tangles-0/cyberdeck-scout/PCB-Resources/models/Infrared Obstacle Detecting Module v4.step

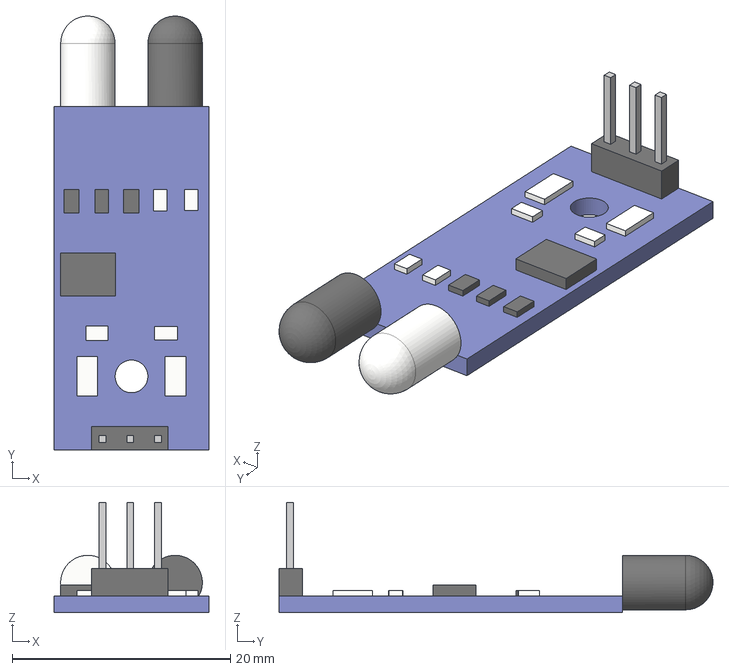
[picture p17: CAD file, 2026-06-25]
PCB-Resources/models/Infrared Obstacle Detecting Module v4.step
14.2 x 39.8 x 10.1 mm
