tangles-0/cyberdeck-scout/PCB-Resources/models/JoyCon Switch Joystick.step

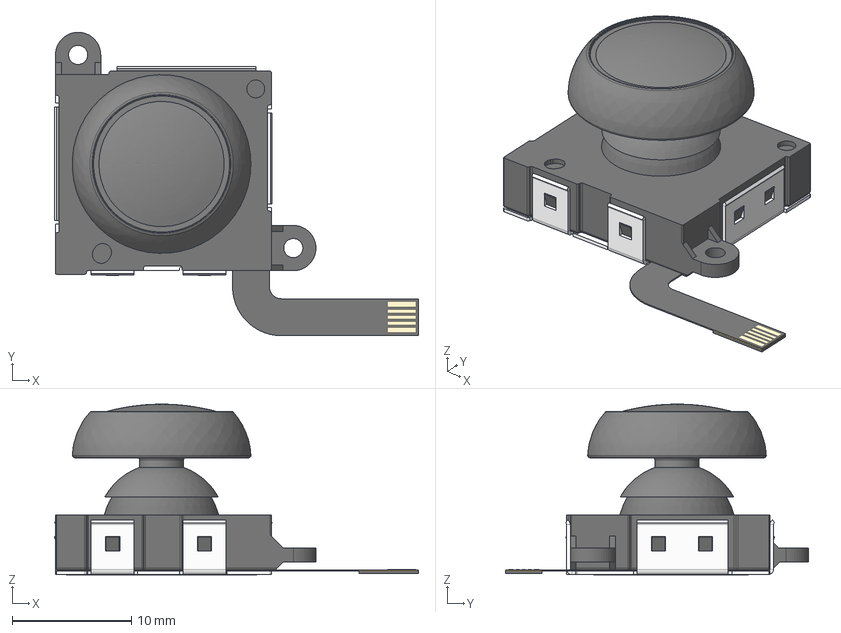
[picture p18: CAD file, 2026-06-25]
PCB-Resources/models/JoyCon Switch Joystick.step
30.5 x 25.5 x 14.3 mm
Handle
Shield
PCB
