tangles-0/cyberdeck-scout/PCB-Resources/models/SIM7100-6-1-15-00-A--3DModel-STEP-56544.STEP

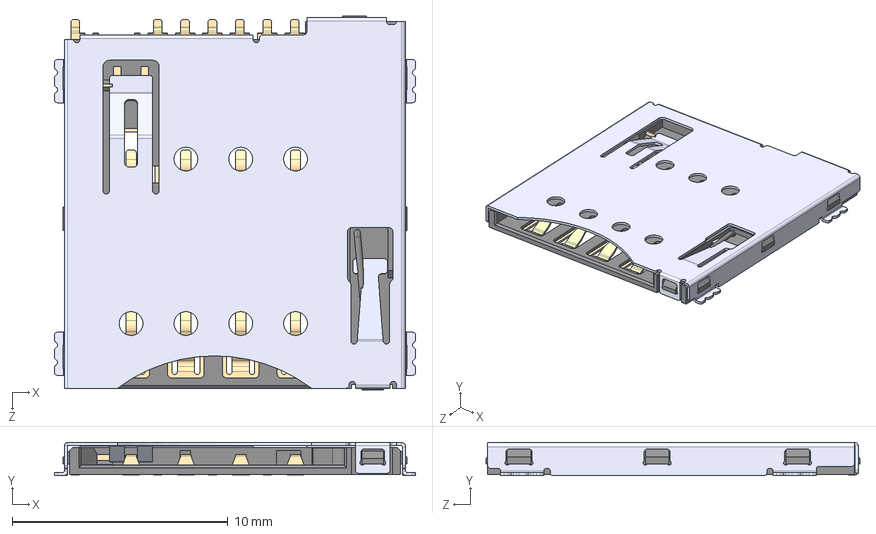
[picture p19: CAD file, 2026-06-25]
PCB-Resources/models/SIM7100-6-1-15-00-A--3DModel-STEP-56544.STEP
16.8 x 1.53 x 17.3 mm
