tangles-0/cyberdeck-scout/PCB-Resources/models/S2B-PH-SM4-TB -LF--SN---3DModel-STEP-269445.STEP

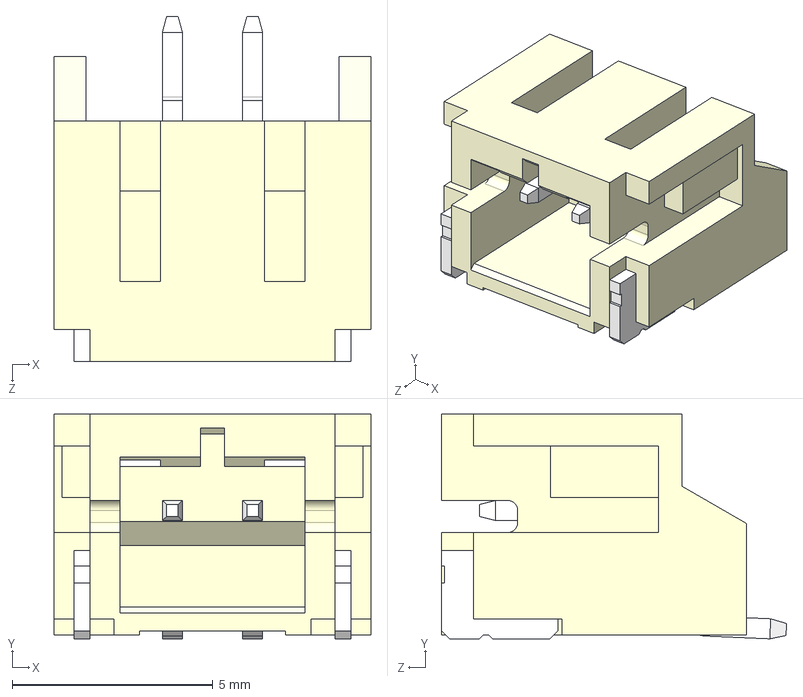
[picture p20: CAD file, 2026-06-25]
PCB-Resources/models/S2B-PH-SM4-TB -LF--SN---3DModel-STEP-269445.STEP
7.90 x 5.60 x 8.60 mm
