tangles-0/cyberdeck-scout/PCB-Resources/models/mini-hdmi-type-C-2013978-2.stp

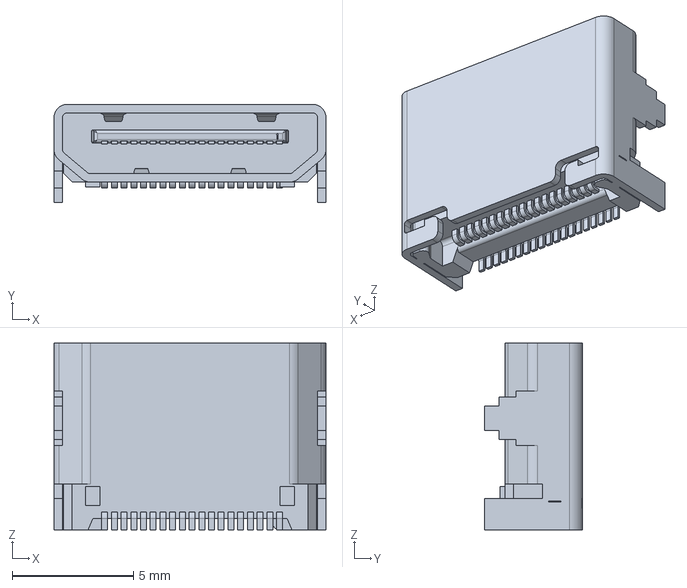
[picture p21: CAD file, 2026-06-25]
PCB-Resources/models/mini-hdmi-type-C-2013978-2.stp
11.2 x 4.05 x 7.70 mm
