tangles-0/cyberdeck-scout/PCB-Resources/models/AFC07-S22FCA-00.stp

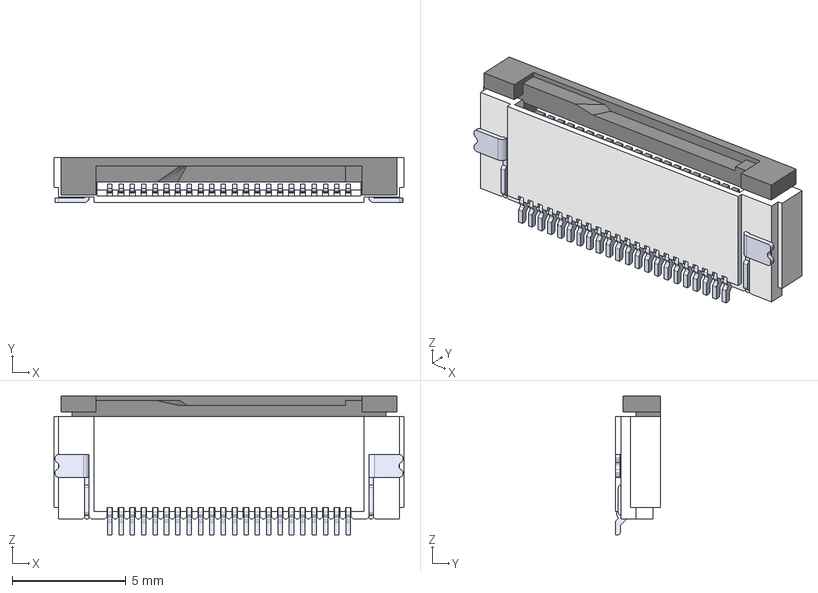
[picture p22: CAD file, 2026-06-25]
PCB-Resources/models/AFC07-S22FCA-00.stp
15.4 x 2.00 x 6.10 mm
