tangles-0/cyberdeck-scout/PCB-Resources/models/modulo heltec ht62_.step

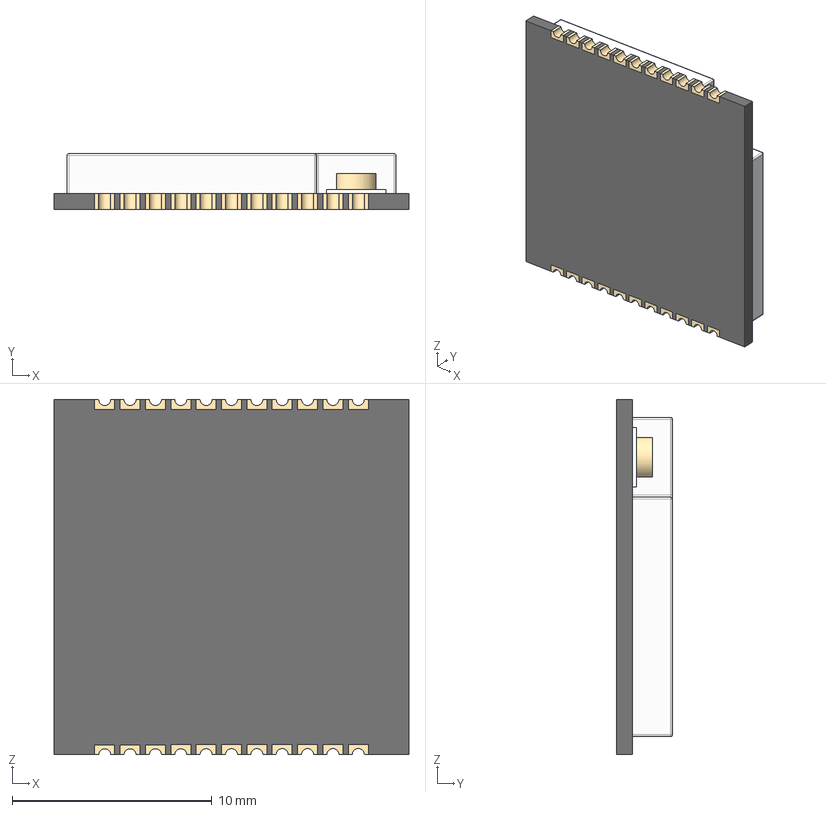
[picture p23: CAD file, 2026-06-25]
PCB-Resources/models/modulo heltec ht62_.step
17.8 x 2.80 x 17.8 mm
