tangles-0/cyberdeck-scout/PCB-Resources/models/WS2812B2020.step

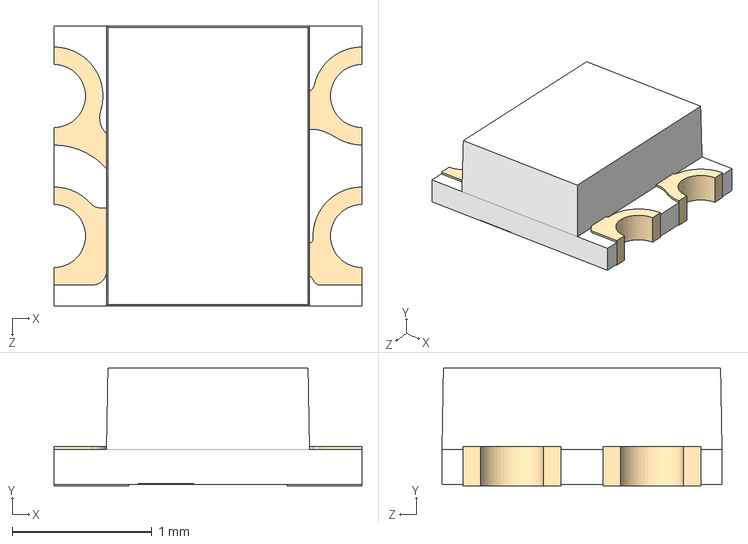
[picture p24: CAD file, 2026-06-25]
PCB-Resources/models/WS2812B2020.step
2.20 x 0.84 x 2.00 mm
