tangles-0/cyberdeck-scout/PCB-Resources/models/BM04B-SRSS-TB.step

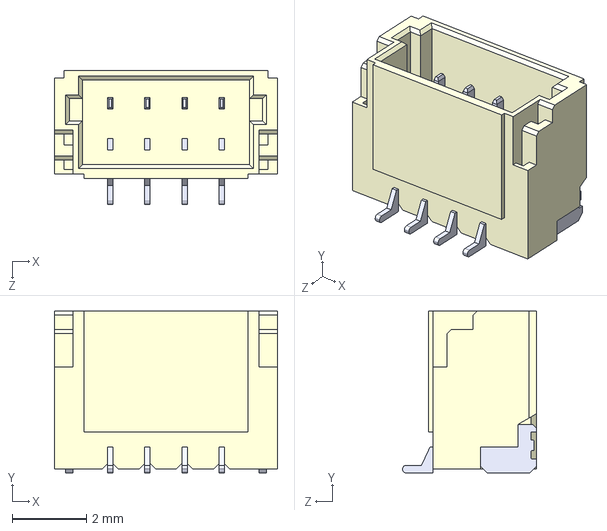
[picture p25: CAD file, 2026-06-25]
PCB-Resources/models/BM04B-SRSS-TB.step
6.00 x 4.35 x 3.60 mm
