tangles-0/cyberdeck-scout/PCB-Resources/models/SSSS811101.step

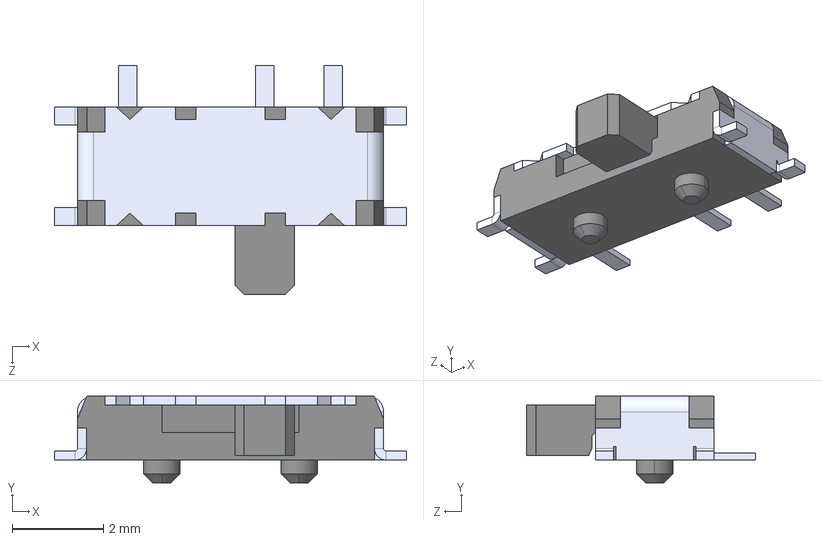
[picture p26: CAD file, 2026-06-25]
PCB-Resources/models/SSSS811101.step
7.70 x 1.90 x 5.00 mm
