tangles-0/cyberdeck-scout/PCB-Resources/models/RCJ-017--3DModel-STEP-1.STEP

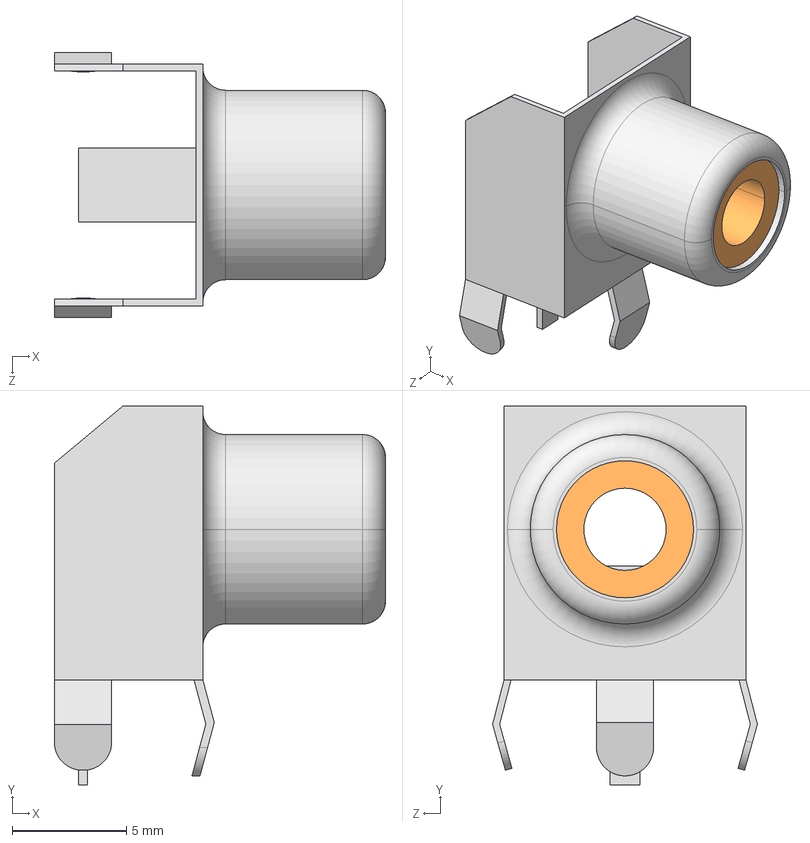
[picture p27: CAD file, 2026-06-25]
PCB-Resources/models/RCJ-017--3DModel-STEP-1.STEP
14.5 x 16.6 x 11.6 mm
