tangles-0/cyberdeck-scout/PCB-Resources/models/SMF05C.step

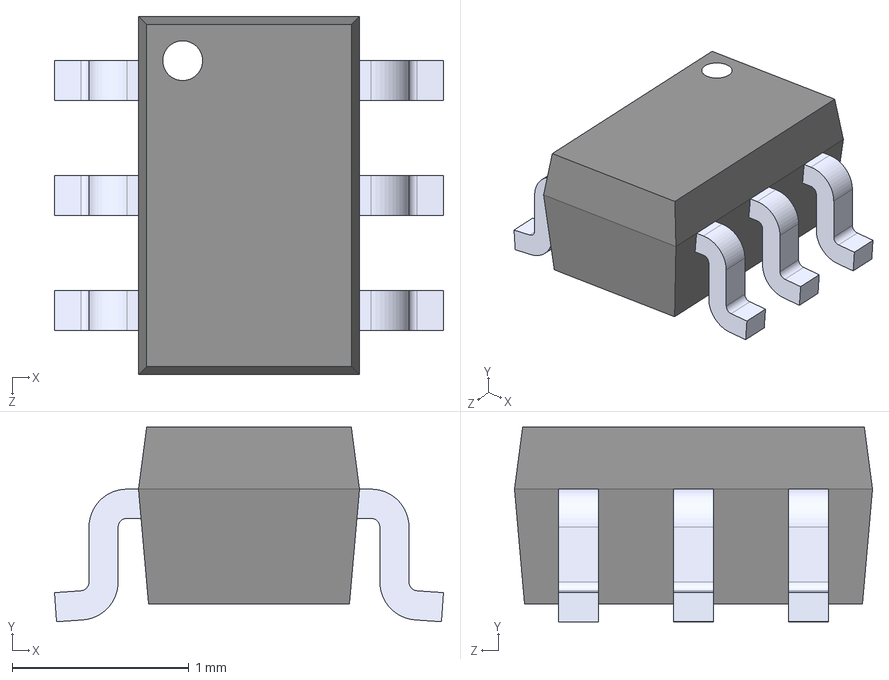
[picture p28: CAD file, 2026-06-25]
PCB-Resources/models/SMF05C.step
2.20 x 1.10 x 2.03 mm
