tangles-0/cyberdeck-scout/PCB-Resources/models/PCM2704CDB.step

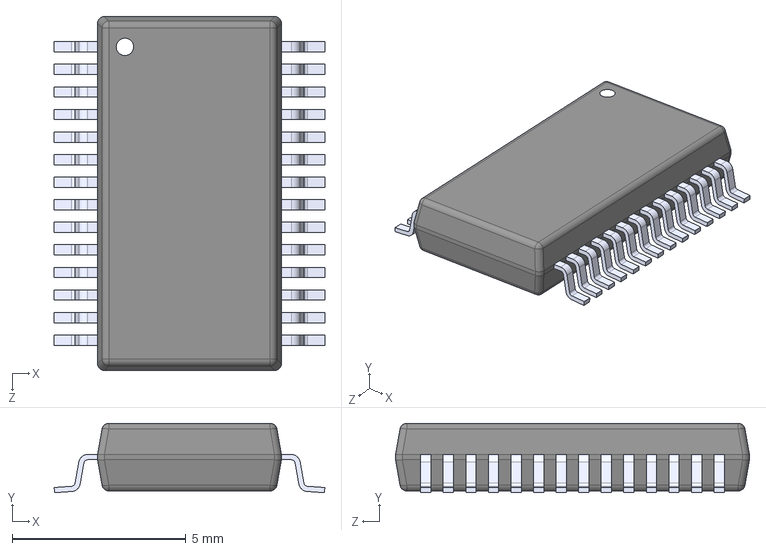
[picture p29: CAD file, 2026-06-25]
PCB-Resources/models/PCM2704CDB.step
7.80 x 2.00 x 10.2 mm
