tangles-0/cyberdeck-scout/PCB-Resources/models/AFC07-S30FCA-00.stp

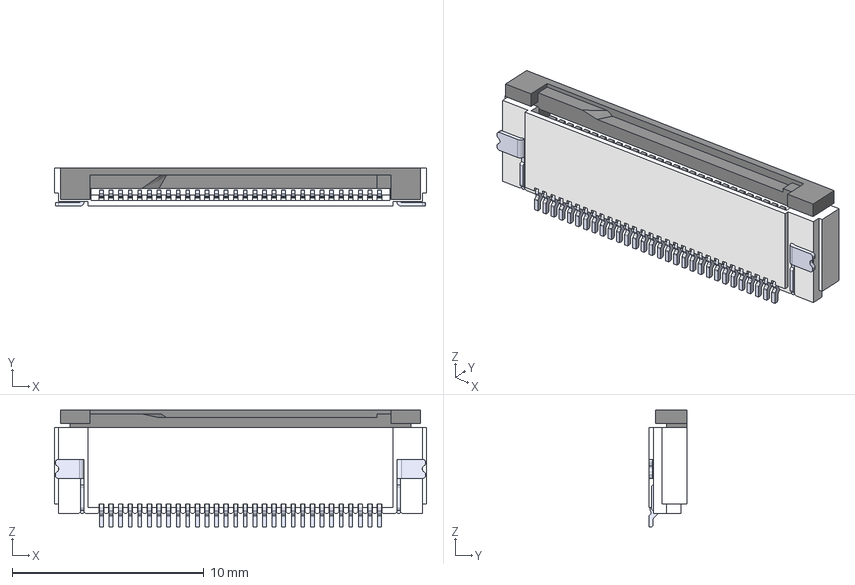
[picture p30: CAD file, 2026-06-25]
PCB-Resources/models/AFC07-S30FCA-00.stp
19.4 x 2.00 x 6.10 mm
