tangles-0/cyberdeck-scout/PCB-Resources/models/QFN40P400X400X100-33N.step

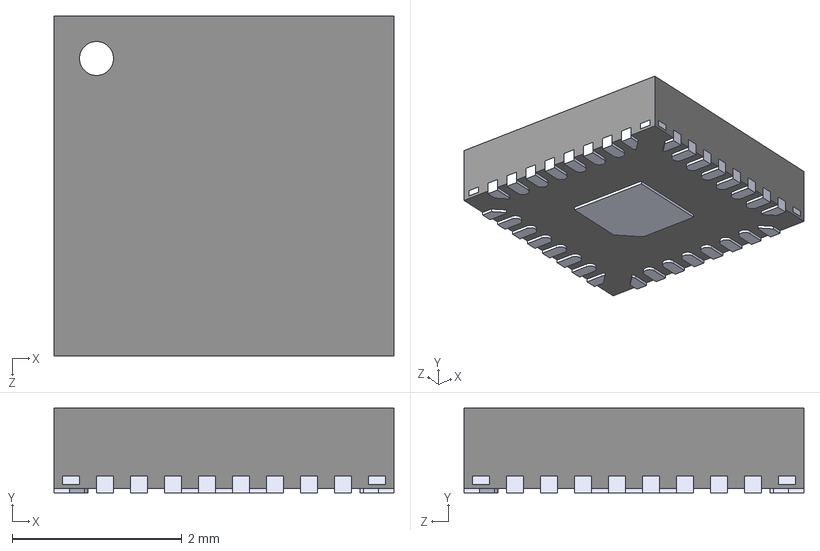
[picture p31: CAD file, 2026-06-25]
PCB-Resources/models/QFN40P400X400X100-33N.step
4.00 x 1.00 x 4.00 mm
