tangles-0/cyberdeck-scout/PCB-Resources/models/1000base-t-magnetics.stp

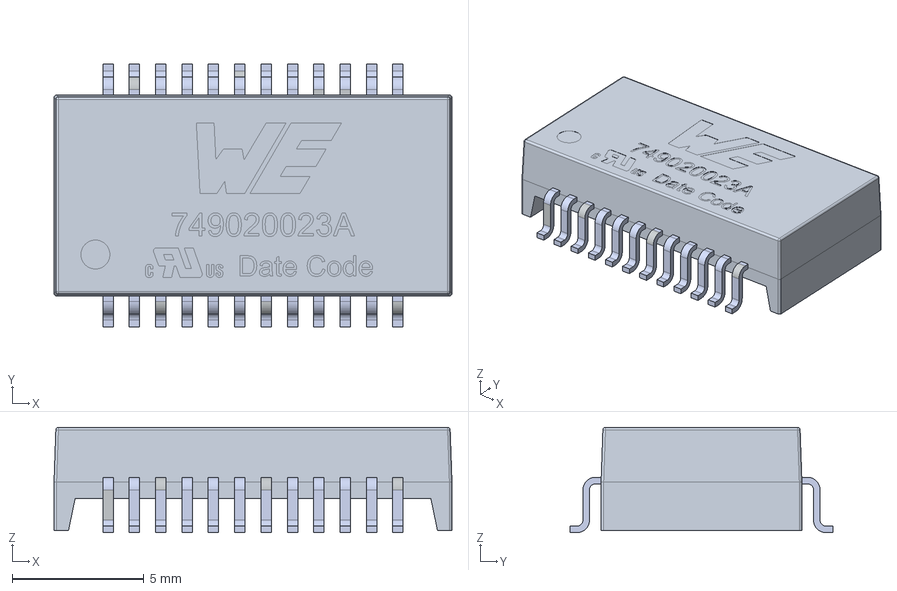
[picture p32: CAD file, 2026-06-25]
PCB-Resources/models/1000base-t-magnetics.stp
15.1 x 10.0 x 4.00 mm
Housing_oa_0
Pins
