tangles-0/cyberdeck-scout/PCB-Resources/models/cyntec_vcmt063t.step

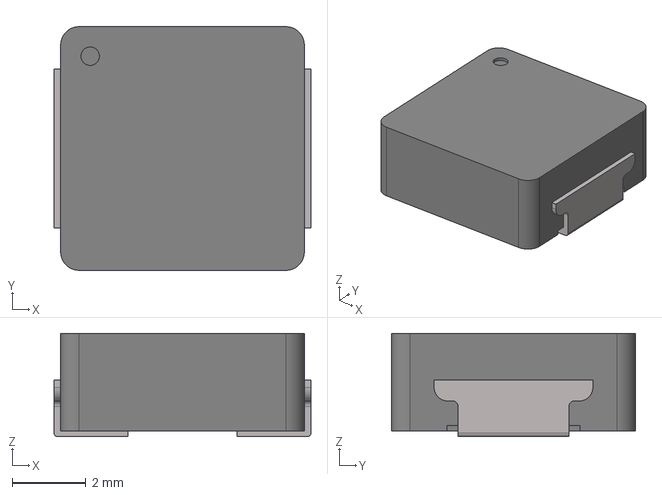
[picture p33: CAD file, 2026-06-25]
PCB-Resources/models/cyntec_vcmt063t.step
6.96 x 6.60 x 2.80 mm
