tangles-0/cyberdeck-scout/PCB-Resources/models/FPC-5.stp

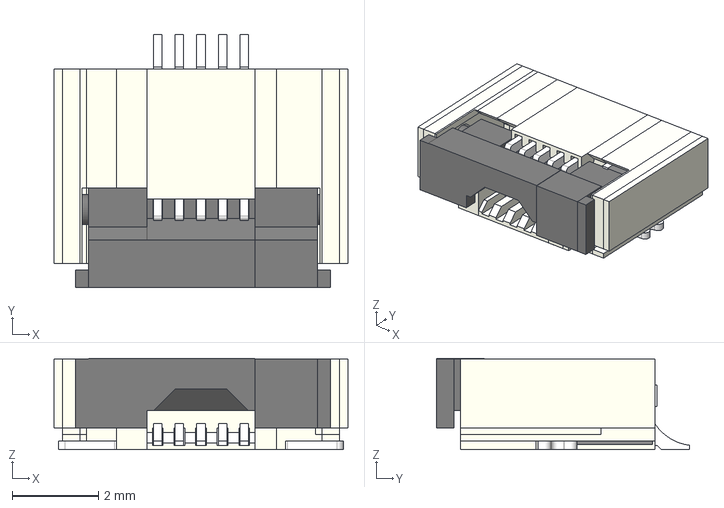
[picture p35: CAD file, 2026-06-25]
PCB-Resources/models/FPC-5.stp
6.80 x 5.85 x 2.11 mm
