tangles-0/cyberdeck-scout/PCB-Resources/models/PspJoystick v5.step

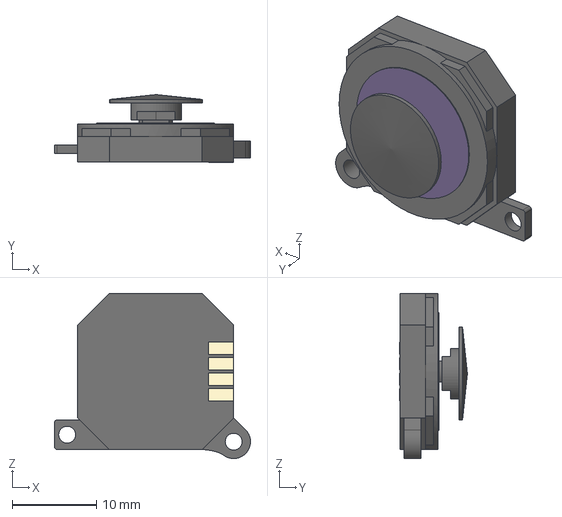
[picture p36: CAD file, 2026-06-25]
PCB-Resources/models/PspJoystick v5.step
23.2 x 8.05 x 19.6 mm
