tangles-0/cyberdeck-scout/PCB-Resources/models/PC817X2NIP1B.step

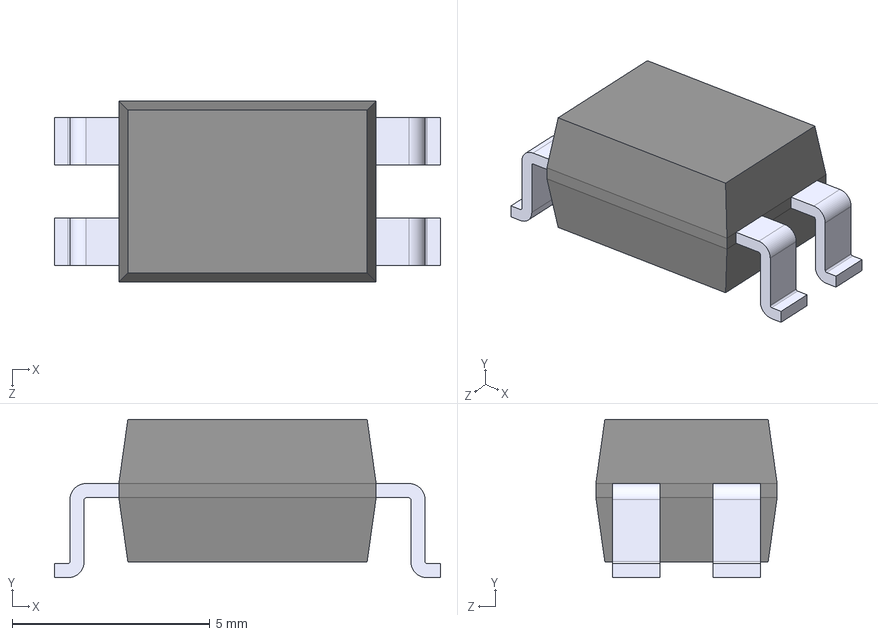
[picture p37: CAD file, 2026-06-25]
PCB-Resources/models/PC817X2NIP1B.step
9.75 x 4.00 x 4.58 mm
