tangles-0/cyberdeck-scout/PCB-Resources/models/PCM2706CPJT.step

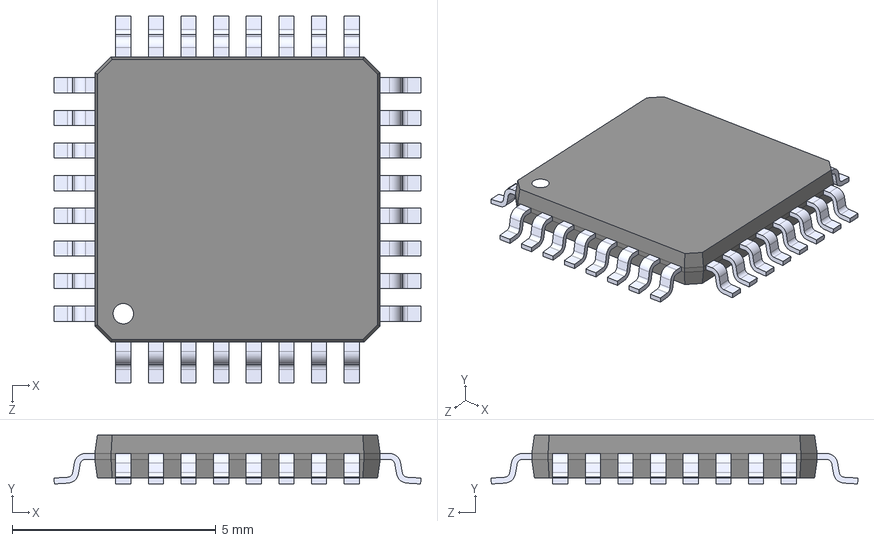
[picture p38: CAD file, 2026-06-25]
PCB-Resources/models/PCM2706CPJT.step
9.00 x 1.20 x 9.00 mm
