tangles-0/cyberdeck-scout/PCB-Resources/models/LQFP_0.5P_100.STEP

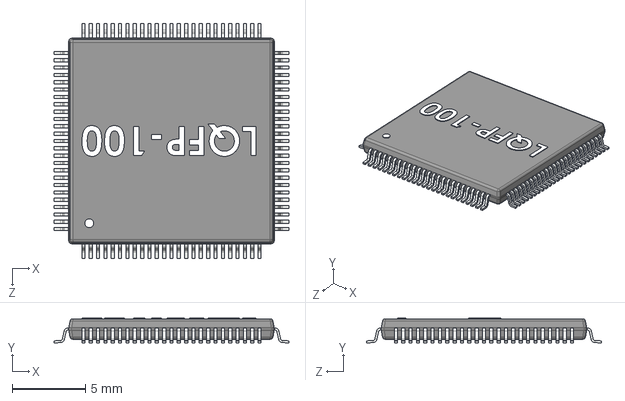
[picture p39: CAD file, 2026-06-25]
PCB-Resources/models/LQFP_0.5P_100.STEP
16.0 x 1.70 x 16.0 mm
