tangles-0/cyberdeck-scout/PCB-Resources/models/TPD2EUSB30DRTR.step

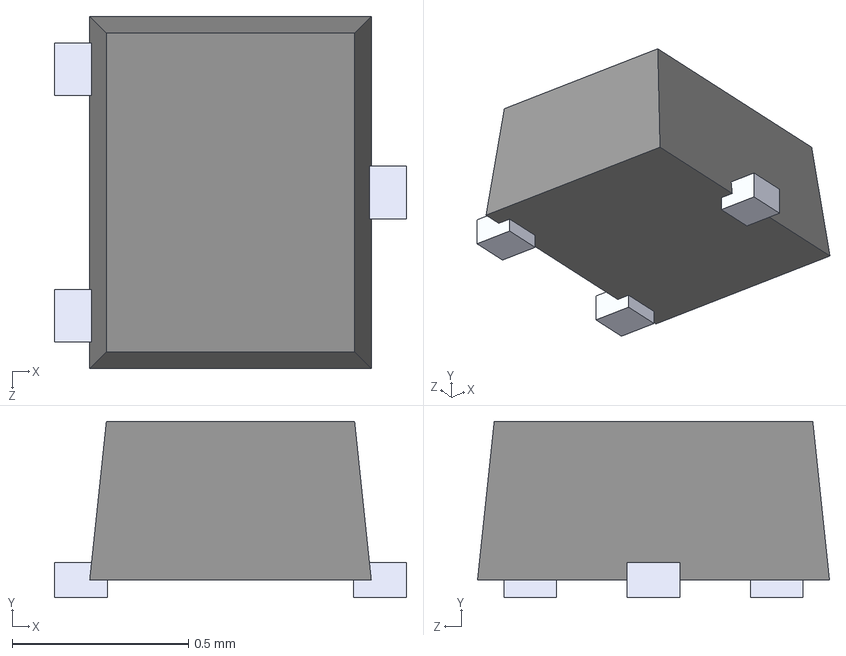
[picture p40: CAD file, 2026-06-25]
PCB-Resources/models/TPD2EUSB30DRTR.step
1.00 x 0.5 x 1.00 mm
