tangles-0/cyberdeck-scout/PCB-Resources/models/PJ311D_WPos.STEP

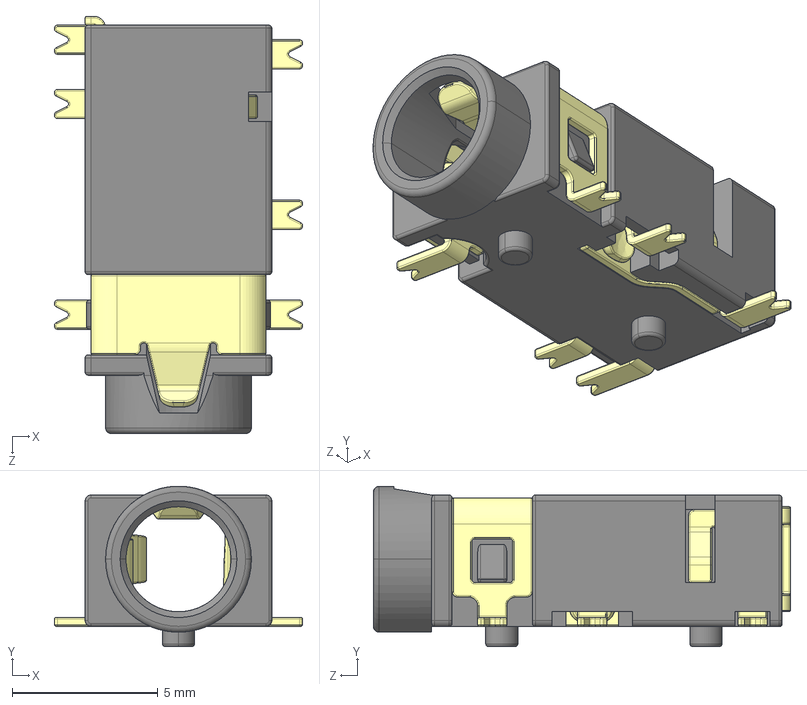
[picture p41: CAD file, 2026-06-25]
PCB-Resources/models/PJ311D_WPos.STEP
8.50 x 5.50 x 14.3 mm
001^PJ311D_WPos
002^PJ311D_WPos
003^PJ311D_WPos
004^PJ311D_WPos
005^PJ311D_WPos
006^PJ311D_WPos
007^PJ311D_WPos
