tangles-0/cyberdeck-scout/PCB-Resources/models/1-2199119-5.step

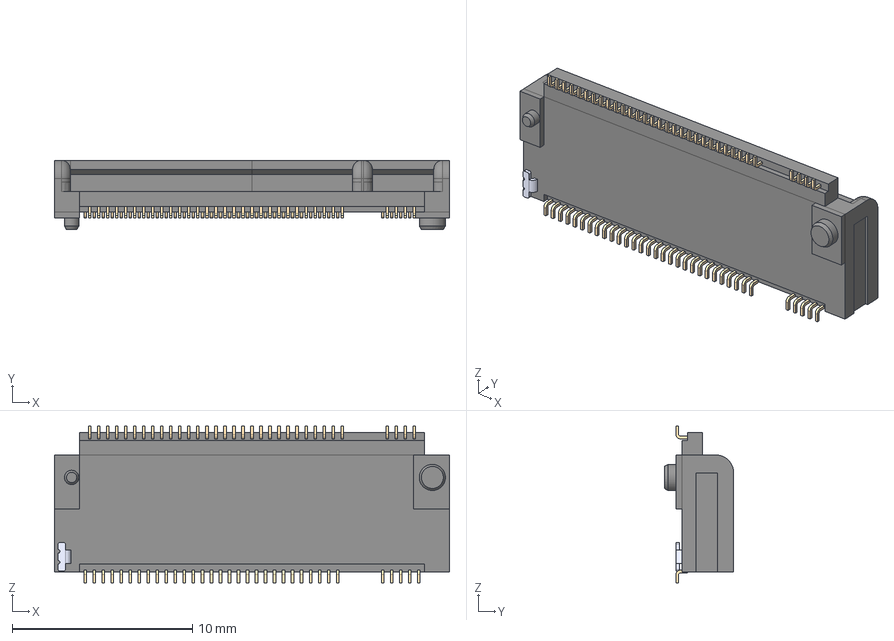
[picture p42: CAD file, 2026-06-25]
PCB-Resources/models/1-2199119-5.step
21.9 x 3.85 x 8.70 mm
Body005 (Mirror #1)
