tangles-0/cyberdeck-scout/PCB-Resources/models/QFN26 4mm X 4mm.STEP

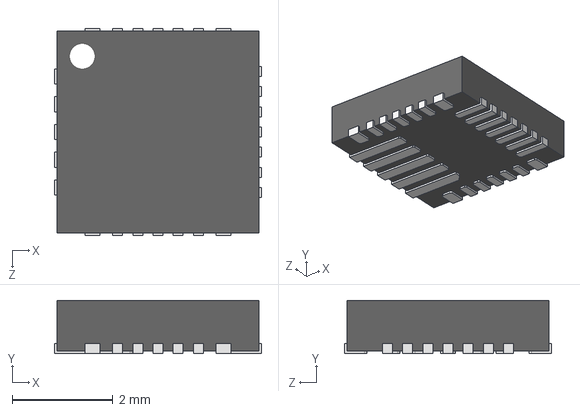
[picture p43: CAD file, 2026-06-25]
PCB-Resources/models/QFN26 4mm X 4mm.STEP
4.10 x 1.05 x 4.10 mm
