tangles-0/cyberdeck-scout/PCB-Resources/models/4_3inch-dsi-lcd-V1.stp

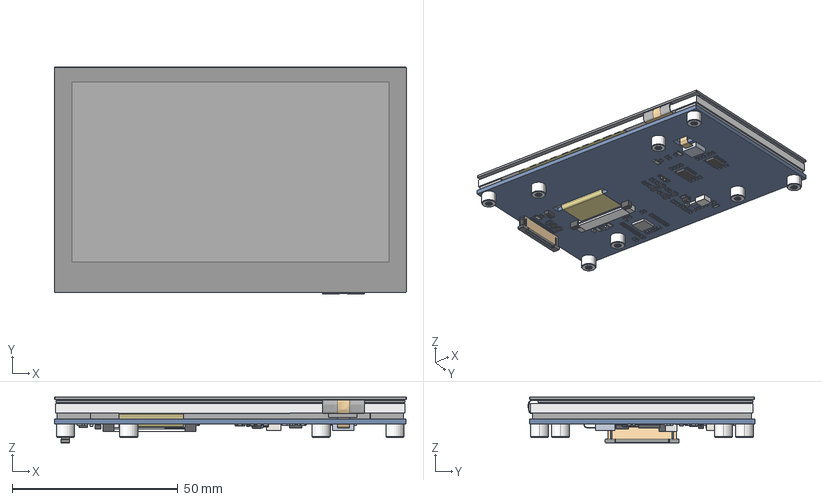
[picture p44: CAD file, 2026-06-25]
PCB-Resources/models/4_3inch-dsi-lcd-V1.stp
106.1 x 68.4 x 13.8 mm
43H-800480-IPS
43H-800480-TP
BOARD
_2_1_2_3_4_AF0 x 2
_7_1_2_AF0 x 2
3_1_2_A x 2
EXTRUDED-91008 x 5
EXTRUDED-91380 x 10
EXTRUDED-91788 x 2
EXTRUDED-92160 x 4
EXTRUDED-92614 x 26
EXTRUDED-92986 x 54
EXTRUDED-93762 x 8
EXTRUDED-94134 x 16
EXTRUDED-95370 x 28
EXTRUDED-95742 x 56
EXTRUDED-96150 x 26
EXTRUDED-96522 x 52
EXTRUDED-96930
EXTRUDED-98589 x 12
EXTRUDED-98961 x 4
EXTRUDED-99531 x 5
EXTRUDED-100568 x 2
EXTRUDED-101876 x 40
EXTRUDED-102630
CIRCUITWORKS-SOD123 x 2
EXTRUDED-106278
EXTRUDED-106739
EXTRUDED-107111 x 2
EXTRUDED-107488
EXTRUDED-107860 x 2
EXTRUDED-108430
EXTRUDED-108972
EXTRUDED-109367 x 3
SMTSO-M2_5-4ET x 8
DISPLAY_CAM
TP-CONNECTOR
EVA-2MM
