tangles-0/cyberdeck-scout/PCB-Resources/models/reverse-mount-LED.STEP

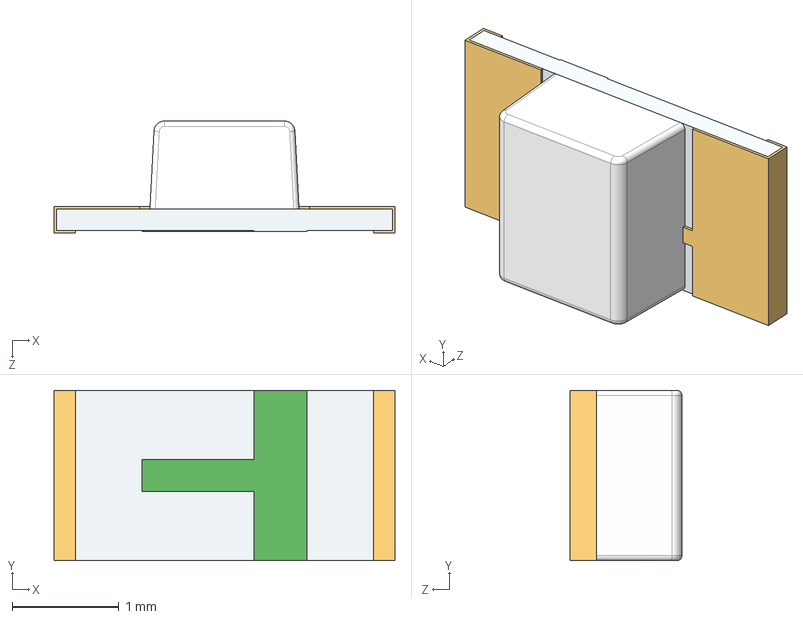
[picture p45: CAD file, 2026-06-25]
PCB-Resources/models/reverse-mount-LED.STEP
3.20 x 1.60 x 1.05 mm
KPTR-3216CGCK
KPTR-3216CGCK-e2
KPTR-3216CGCK-g
KPTR-3216CGCK-e
