tangles-0/cyberdeck-scout/PCB-Resources/models/B2B-PH-SM4-TB--3DModel-STEP-418109.STEP

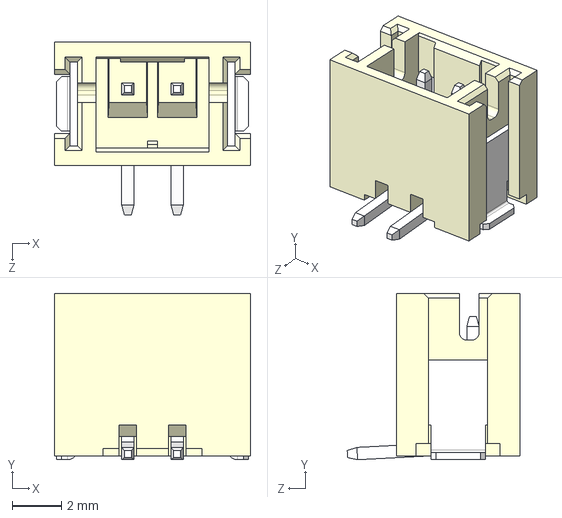
[picture p46: CAD file, 2026-06-25]
PCB-Resources/models/B2B-PH-SM4-TB--3DModel-STEP-418109.STEP
7.95 x 6.75 x 7.00 mm
