tangles-0/cyberdeck-scout/PCB-Resources/models/RAK4630.step

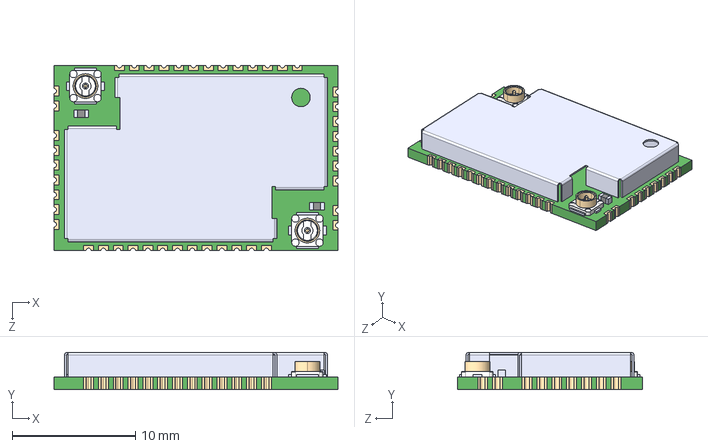
[picture p47: CAD file, 2026-06-25]
PCB-Resources/models/RAK4630.step
23.0 x 3.00 x 15.0 mm
