tangles-0/cyberdeck-scout/PCB-Resources/models/ss-12d11g5r.stp

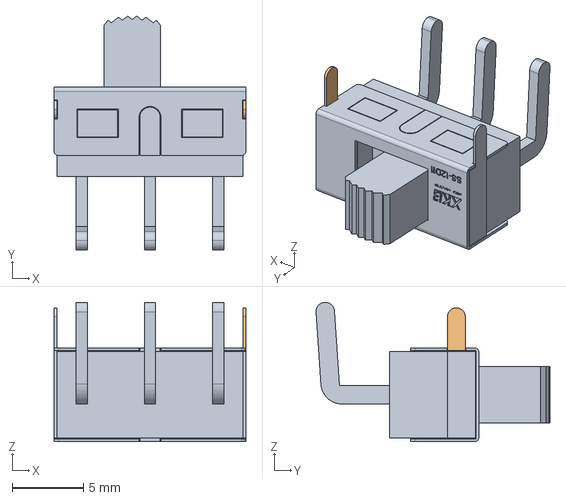
[picture p48: CAD file, 2026-06-25]
PCB-Resources/models/ss-12d11g5r.stp
13.5 x 16.4 x 9.80 mm
