tangles-0/cyberdeck-scout/PCB-Resources/models/QFN-28 (4x4x0.9).step

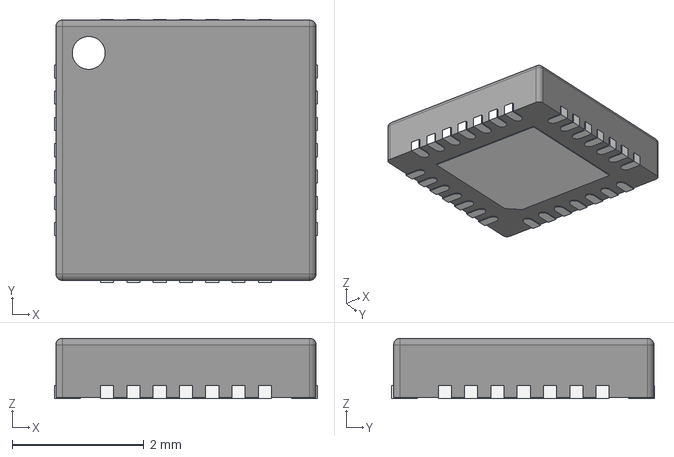
[picture p49: CAD file, 2026-06-25]
PCB-Resources/models/QFN-28 (4x4x0.9).step
4.00 x 4.00 x 0.92 mm
