tangles-0/cyberdeck-scout/PCB-Resources/models/TS-1088-AR02016--3DModel-STEP-269445.STEP

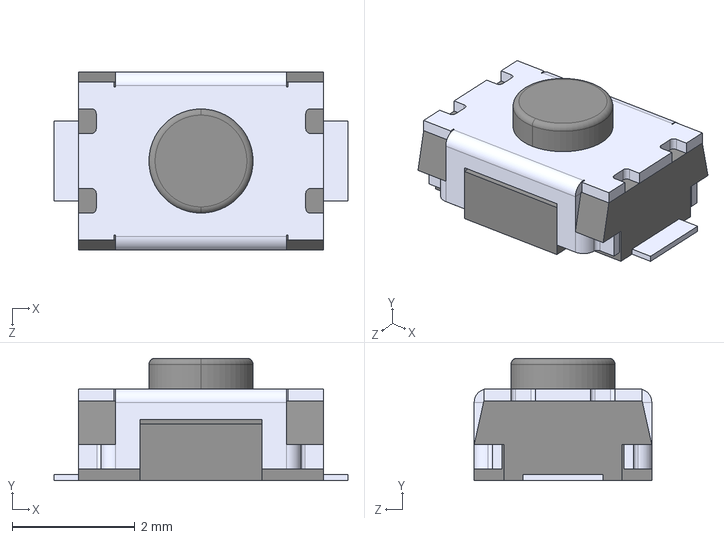
[picture p50: CAD file, 2026-06-25]
PCB-Resources/models/TS-1088-AR02016--3DModel-STEP-269445.STEP
4.80 x 2.00 x 2.90 mm
