tangles-0/cyberdeck-scout/PCB-Resources/models/SO-8EP.STP

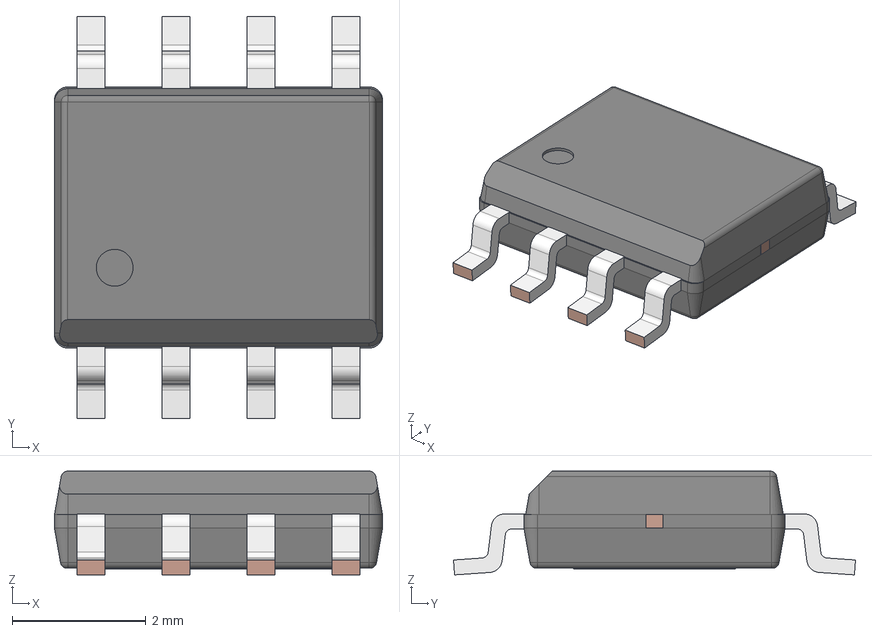
[picture p51: CAD file, 2026-06-25]
PCB-Resources/models/SO-8EP.STP
4.90 x 6.00 x 1.55 mm
CPD
LDF - outer lead
LDF - 8L-EP
