tangles-0/cyberdeck-scout/PCB-Resources/models/2-1734839-0.stp

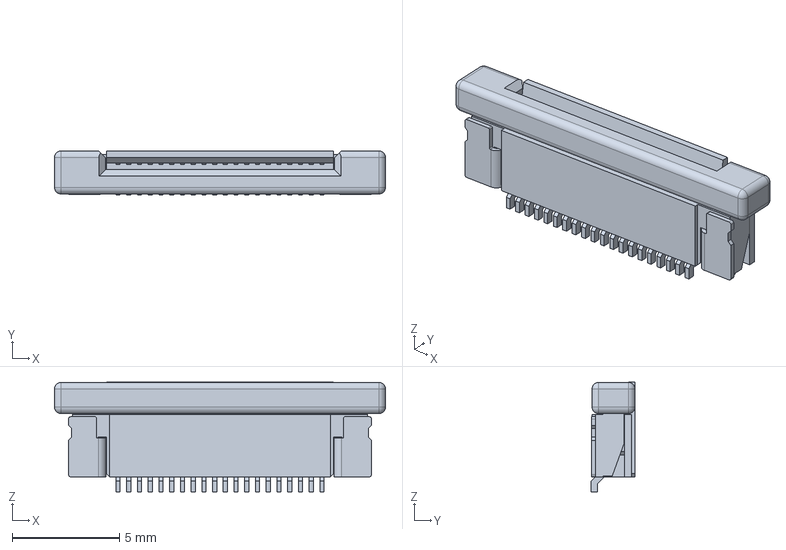
[picture p52: CAD file, 2026-06-25]
PCB-Resources/models/2-1734839-0.stp
15.4 x 2.05 x 5.11 mm
