tangles-0/cyberdeck-scout/PCB-Resources/models/Keystone10mmDiaDomePB v2.step

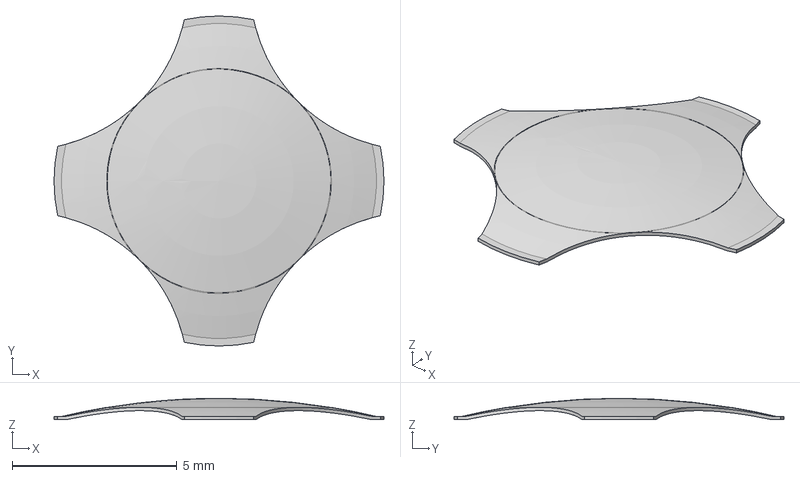
[picture p53: CAD file, 2026-06-25]
PCB-Resources/models/Keystone10mmDiaDomePB v2.step
10.0 x 10.0 x 0.65 mm
