tangles-0/cyberdeck-scout/PCB-Resources/models/TPD4EUSB30DQAR.step

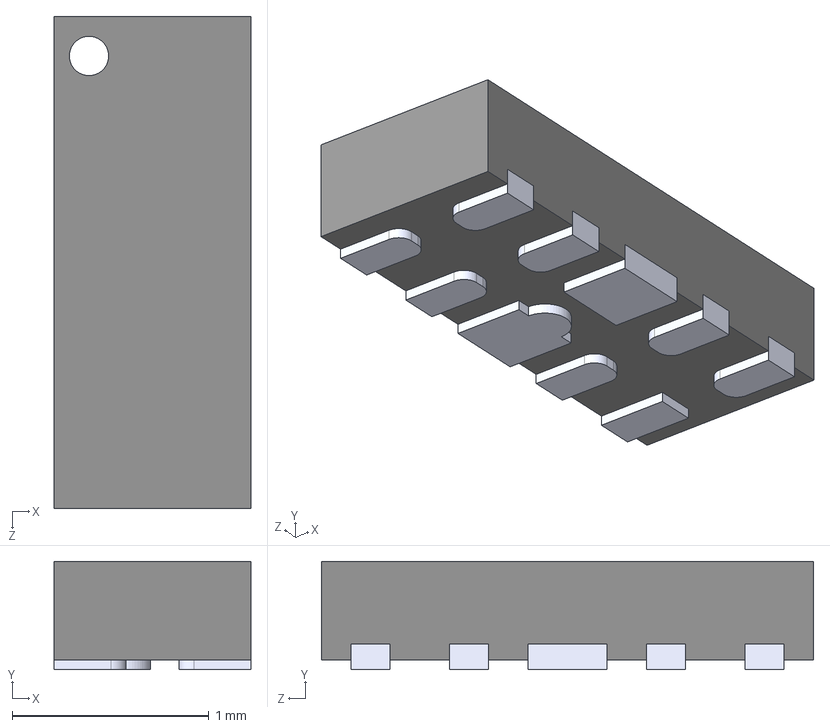
[picture p54: CAD file, 2026-06-25]
PCB-Resources/models/TPD4EUSB30DQAR.step
1.00 x 0.55 x 2.50 mm
