tangles-0/cyberdeck-scout/PCB-Resources/models/QFN26-3.5x3.5-MP2723GQC.step

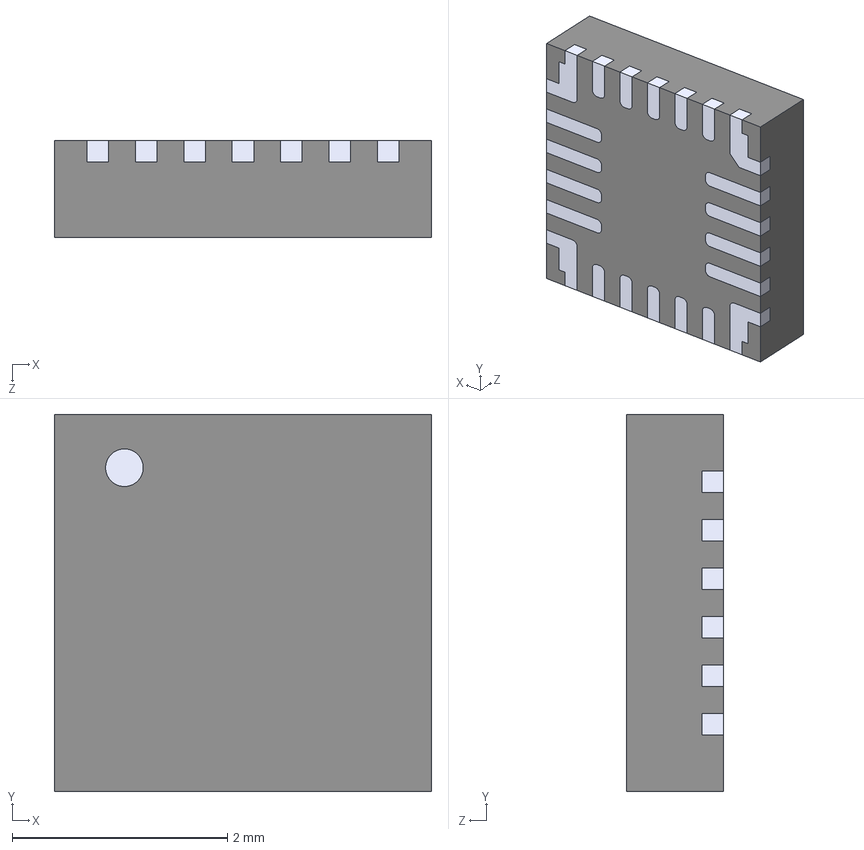
[picture p55: CAD file, 2026-06-25]
PCB-Resources/models/QFN26-3.5x3.5-MP2723GQC.step
3.50 x 3.50 x 0.9 mm
