tangles-0/cyberdeck-scout/PCB-Resources/models/FTE-121-01-G-DH-K.stp

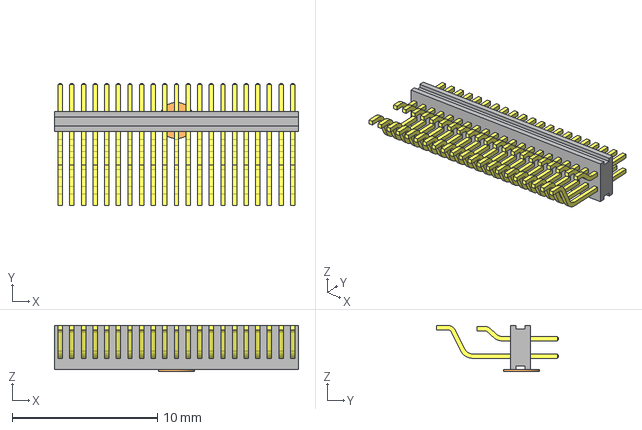
[picture p56: CAD file, 2026-06-25]
PCB-Resources/models/FTE-121-01-G-DH-K.stp
16.8 x 8.38 x 3.20 mm
FTE-121-01-G-DH-K_body
FTE-121-01-G-DH-K_pins
