tangles-0/cyberdeck-scout/PCB-Resources/models/HRO_TYPE-C-31-M-12.step

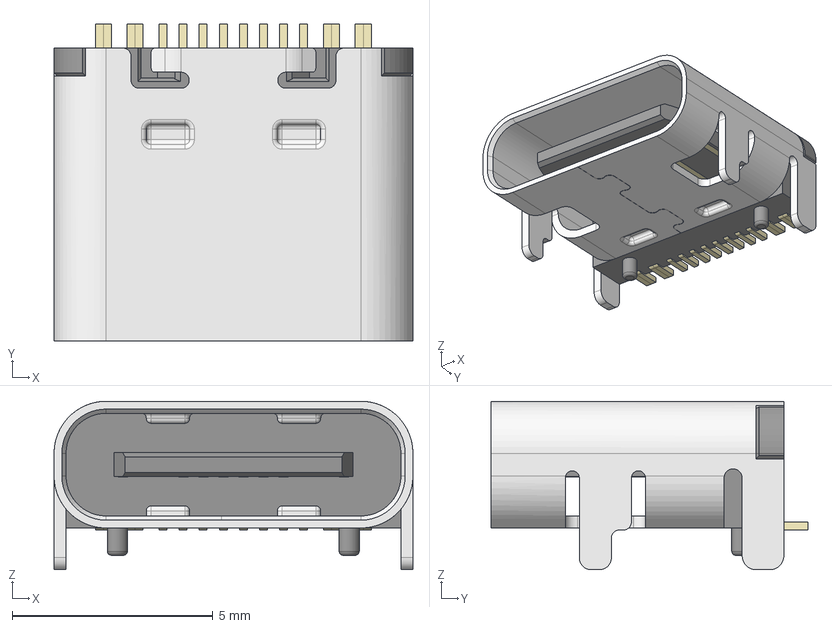
[picture p57: CAD file, 2026-06-25]
PCB-Resources/models/HRO_TYPE-C-31-M-12.step
8.95 x 7.90 x 4.20 mm
