tangles-0/cyberdeck-scout/PCB-Resources/models/DM3AT-SF-PEJM5.step

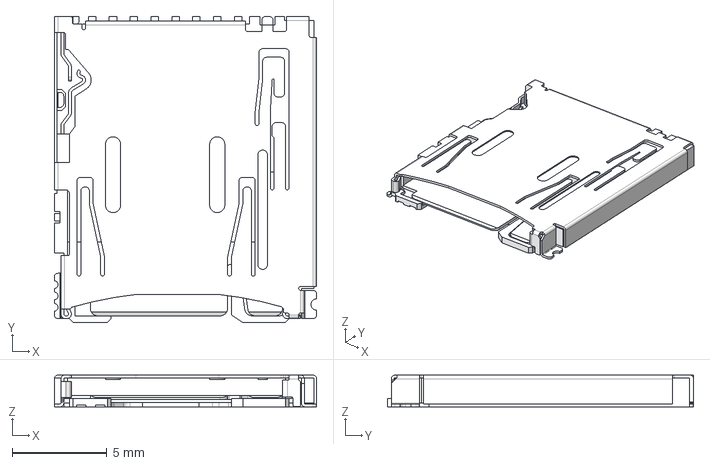
[picture p58: CAD file, 2026-06-25]
PCB-Resources/models/DM3AT-SF-PEJM5.step
13.8 x 16.2 x 1.68 mm
