tangles-0/cyberdeck-scout/PCB-Resources/models/AFC07-S05FCA-00.stp

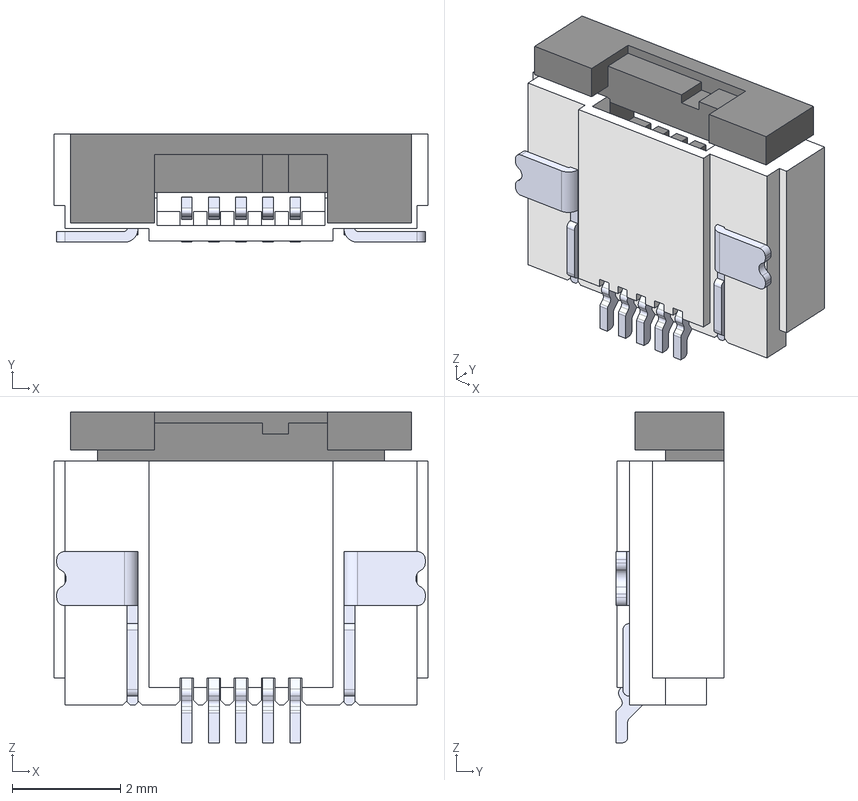
[picture p59: CAD file, 2026-06-25]
PCB-Resources/models/AFC07-S05FCA-00.stp
6.90 x 2.00 x 6.10 mm
