tangles-0/cyberdeck-scout/PCB-Resources/models/TL 3330 Tactile Button.stp

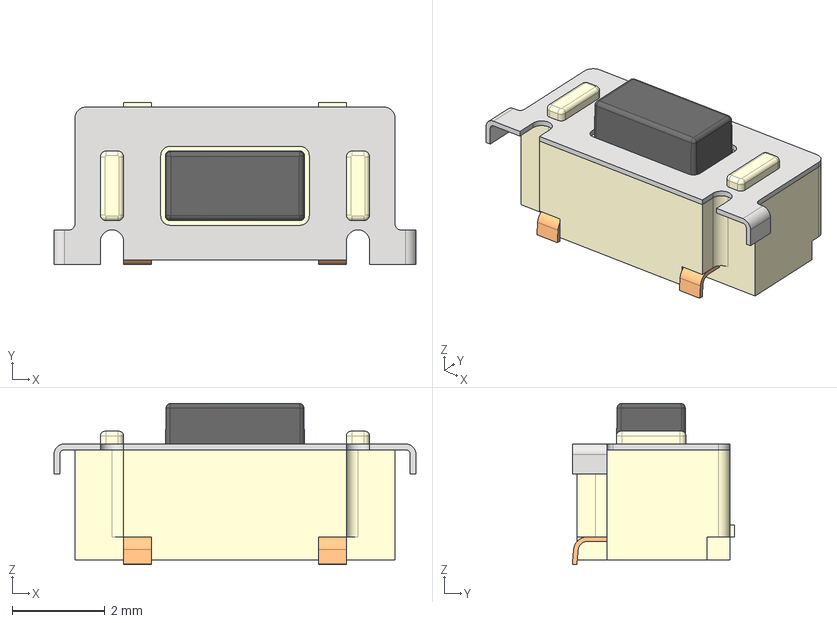
[picture p60: CAD file, 2026-06-25]
PCB-Resources/models/TL 3330 Tactile Button.stp
7.80 x 3.50 x 3.48 mm
