tangles-0/cyberdeck-scout/PCB-Resources/models/MP2632B.step

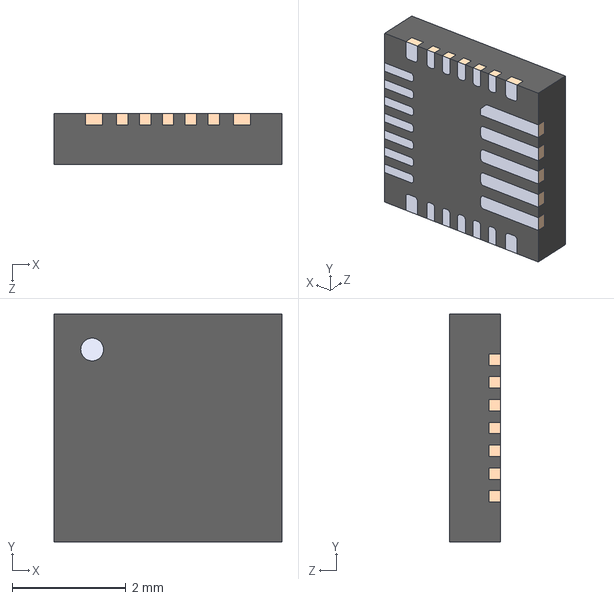
[picture p61: CAD file, 2026-06-25]
PCB-Resources/models/MP2632B.step
4.00 x 4.00 x 0.9 mm
