tangles-0/cyberdeck-scout/PCB-Resources/models/XFL4020-102MEC.step

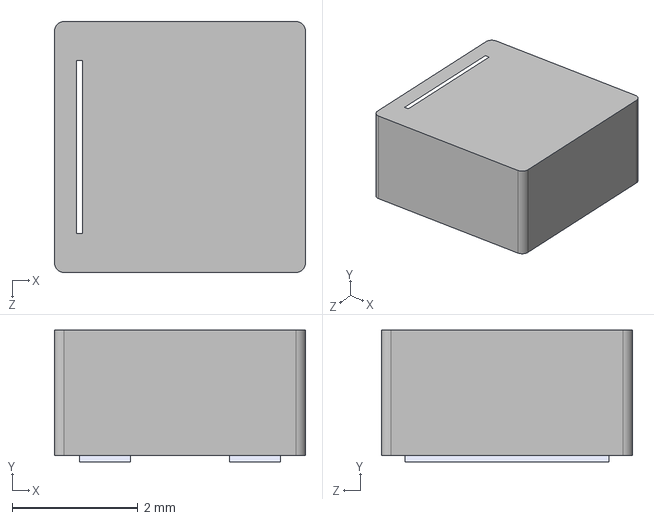
[picture p62: CAD file, 2026-06-25]
PCB-Resources/models/XFL4020-102MEC.step
4.00 x 2.10 x 4.00 mm
