tangles-0/cyberdeck-scout/PCB-Resources/models/AFC01-S40FCA-00.step

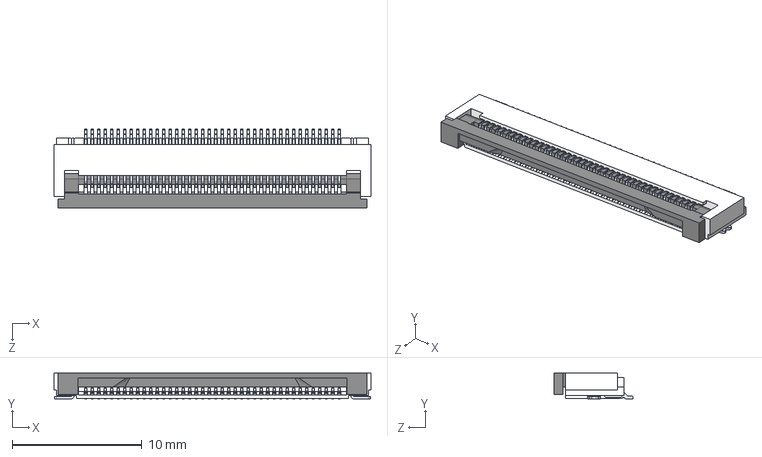
[picture p63: CAD file, 2026-06-25]
PCB-Resources/models/AFC01-S40FCA-00.step
24.4 x 2.00 x 6.10 mm
