tangles-0/cyberdeck-scout/PCB-Resources/models/RK10J1_E.STEP

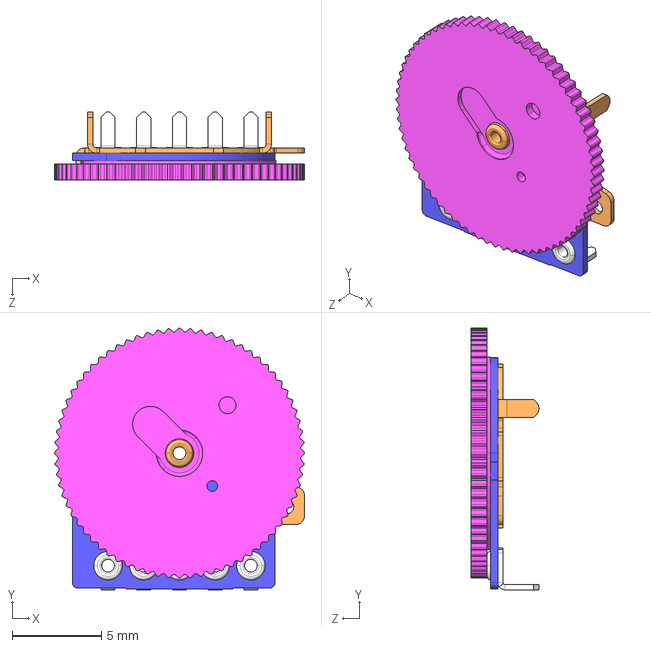
[picture p64: CAD file, 2026-06-25]
PCB-Resources/models/RK10J1_E.STEP
14.0 x 14.6 x 3.80 mm
