tangles-0/cyberdeck-scout/PCB-Resources/models/TUSB8042AIRGCR.step

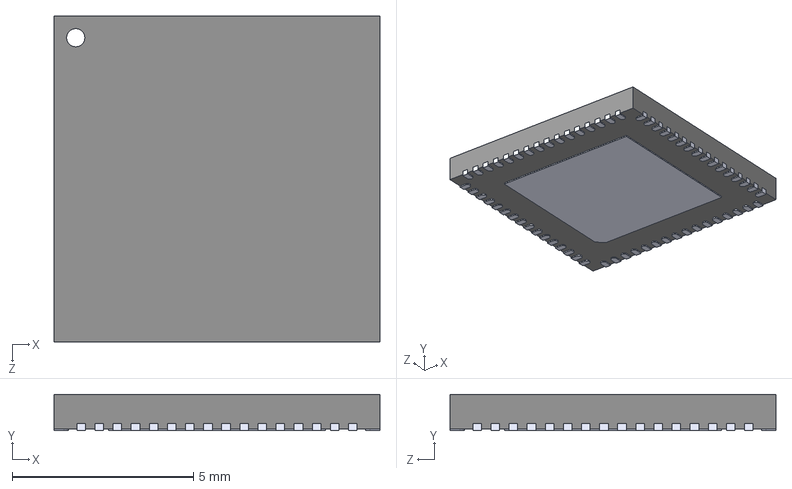
[picture p65: CAD file, 2026-06-25]
PCB-Resources/models/TUSB8042AIRGCR.step
9.00 x 1.00 x 9.00 mm
