tangles-0/cyberdeck-scout/Firmware/qmk/keyboards/rii/518bt/518bt.c

/* Copyright 2017 WoodKeys
*
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
* You should have received a copy of the GNU General Public License
* along with this program.  If not, see <http://www.gnu.org/licenses/>.
*/

#include "518bt.h"

#define USER_LED_1 B2
#define USER_LED_2 B10
#define USER_LED_3 B11

void keyboard_pre_init_kb(void) {
    gpio_set_pin_output(USER_LED_1);
    gpio_set_pin_output(USER_LED_2);
    gpio_set_pin_output(USER_LED_3);
    gpio_write_pin_low(USER_LED_1);
    gpio_write_pin_low(USER_LED_2);
    gpio_write_pin_low(USER_LED_3);
    keyboard_pre_init_user();
}

inline void user_led_on(uint8_t led) {
    switch (led) {
        case 0:
            gpio_write_pin_high(USER_LED_1);
            break;
        case 1:
            gpio_write_pin_high(USER_LED_2);
            break;
        case 2:
            gpio_write_pin_high(USER_LED_3);
            break;
    }
}

inline void user_led_off(uint8_t led) {
    switch (led) {
        case 0:
            gpio_write_pin_low(USER_LED_1);
            break;
        case 1:
            gpio_write_pin_low(USER_LED_2);
            break;
        case 2:
            gpio_write_pin_low(USER_LED_3);
            break;
    }
}
